Bleuarff/teddy-clock/tests/esp_wifi/esp_wifi.ino

// Demo how to set ESP8266 as Access Point with its own network

#include <ESP8266WiFi.h>

void setup()
{
  Serial.begin(115200);
  Serial.println();

  Serial.print("Setting soft-AP ... ");
  boolean result = WiFi.softAP("Teddy-clock", "gabuzomeu");
  if(result == true)
  {
    Serial.println("Ready");
  }
  else
  {
    Serial.println("Failed!");
  }
}

void loop()
{
  Serial.printf("Stations connected = %d\n", WiFi.softAPgetStationNum());
  delay(5000);
}
